hephaestushex/keystroke/schematic/keystroke.kicad_sch

## KiCad design schematic/keystroke.kicad_sch (2026-07-16)

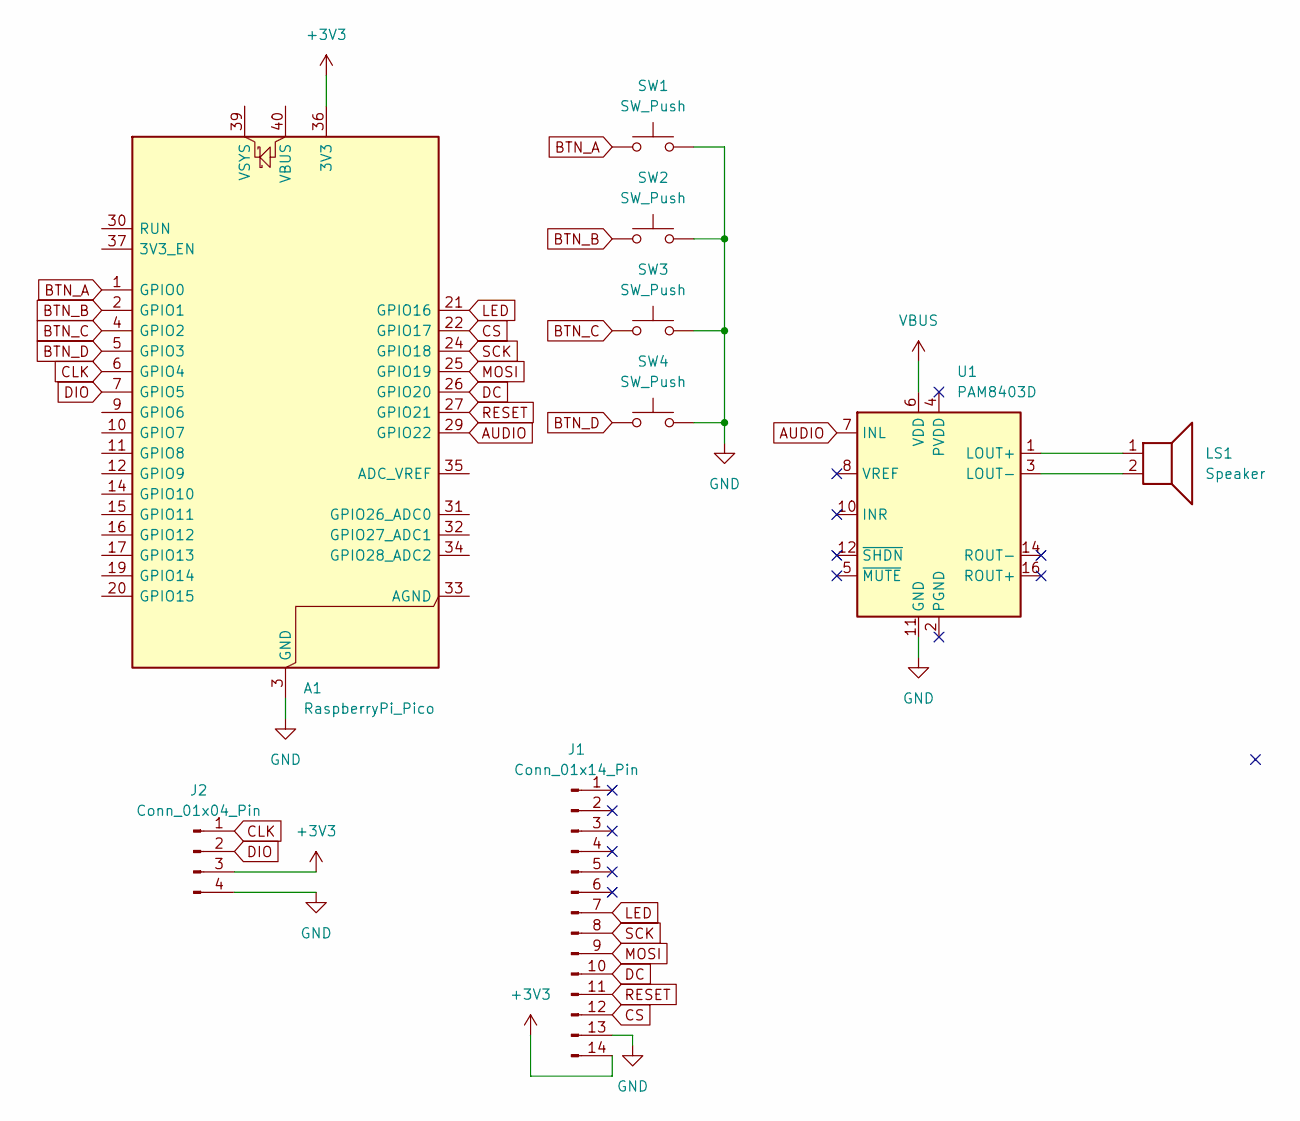
[picture p2: schematic keystroke.kicad_sch]

Parts:
A1: RaspberryPi_Pico; RaspberryPi_Pico_Common_Unspecified
J1: Conn_01x14_Pin
J2: Conn_01x04_Pin
LS1: Speaker
SW1, SW2, SW3, SW4: SW_Push
U1: PAM8403D; SOIC-16_3.9x9.9mm_P1.27mm

Connections:
+3V3: A1.36 (3V3), J1.14, J2.3
AUDIO: A1.29 (GPIO22), U1.7 (INL)
BTN_A: A1.1 (GPIO0), SW1.1
BTN_B: A1.2 (GPIO1), SW2.1
BTN_C: A1.4 (GPIO2), SW3.1
BTN_D: A1.5 (GPIO3), SW4.1
CLK: A1.6 (GPIO4), J2.1
CS: A1.22 (GPIO17), J1.12
DC: A1.26 (GPIO20), J1.10
DIO: A1.7 (GPIO5), J2.2
GND: A1.3 (GND), A1.8 (GND), A1.13 (GND), A1.18 (GND), A1.23 (GND), A1.28 (GND), A1.38 (GND), J1.13, J2.4, SW1.2, SW2.2, SW3.2, SW4.2, U1.11 (GND)
LED: A1.21 (GPIO16), J1.7
MOSI: A1.25 (GPIO19), J1.9
unnamed: LS1.1, U1.1 (LOUT+)
unnamed: LS1.2, U1.3 (LOUT-)
unnamed: U1.4 (PVDD), U1.13 (PVDD)
unnamed: U1.2 (PGND), U1.15 (PGND)
RESET: A1.27 (GPIO21), J1.11
SCK: A1.24 (GPIO18), J1.8
VBUS: U1.6 (VDD)
